Xinyuan-LilyGO/T-Keyboard-S3/examples/Keyboard/Keyboard.ino

#include <Arduino.h>
#include "T-Keyboard_S3_Drive.h"
#include "pin_config.h"
#include "FastLED.h"
#include <USB.h>
#include <USBHIDKeyboard.h>

#define KEY1_SET KEY_LEFT_CTRL
#define KEY2_SET 'c'
#define KEY3_SET 'v'
#define KEY4_SET KEY_BACKSPACE

// #define KEY1_SET 'd'
// #define KEY2_SET 'f'
// #define KEY3_SET 'j'
// #define KEY4_SET 'k'

// How many leds in your strip?
#define NUM_LEDS 4

#define DATA_PIN WS2812B_DATA

// Define the array of leds
CRGB leds[NUM_LEDS];

USBHIDKeyboard Keyboard;

uint8_t KEY1_Lock = 0;
uint8_t KEY1_Press_Delay = 0;
uint8_t KEY2_Lock = 0;
uint8_t KEY2_Press_Delay = 0;
uint8_t KEY3_Lock = 0;
uint8_t KEY3_Press_Delay = 0;
uint8_t KEY4_Lock = 0;
uint8_t KEY4_Press_Delay = 0;

void WS2812B_KEY_Loop(void)
{
    switch (Key1_Flag)
    {
    case 0:
        leds[0] = CRGB::Black;
        FastLED.show();

        Keyboard.release(KEY1_SET);
        KEY1_Press_Delay = 0;
        KEY1_Lock = 0;
        break;
    case 1:
        if (KEY1_Lock == 0)
        {
            leds[0] = CRGB::White;
            FastLED.show();
            Keyboard.press(KEY1_SET);
        }

        if (KEY1_Press_Delay >= 100)
        {
            KEY1_Press_Delay = 100;
            Keyboard.press(KEY1_SET);
        }
        KEY1_Press_Delay++;
        KEY1_Lock = 1;
        break;

    default:
        break;
    }

    switch (Key2_Flag)
    {
    case 0:
        leds[1] = CRGB::Black;
        FastLED.show();

        Keyboard.release(KEY2_SET);
        KEY2_Press_Delay = 0;
        KEY2_Lock = 0;
        break;
    case 1:
        if (KEY2_Lock == 0)
        {
            leds[1] = CRGB::White;
            FastLED.show();
            Keyboard.press(KEY2_SET);
        }

        if (KEY2_Press_Delay >= 100)
        {
            KEY2_Press_Delay = 100;
            Keyboard.press(KEY2_SET);
        }
        KEY2_Press_Delay++;
        KEY2_Lock = 1;
        break;

    default:
        break;
    }

    switch (Key3_Flag)
    {
    case 0:
        leds[2] = CRGB::Black;
        FastLED.show();

        Keyboard.release(KEY3_SET);
        KEY3_Press_Delay = 0;
        KEY3_Lock = 0;
        break;
    case 1:
        if (KEY3_Lock == 0)
        {
            leds[2] = CRGB::White;
            FastLED.show();
            Keyboard.press(KEY3_SET);
        }

        if (KEY3_Press_Delay >= 100)
        {
            KEY3_Press_Delay = 100;
            Keyboard.press(KEY3_SET);
        }
        KEY3_Press_Delay++;
        KEY3_Lock = 1;
        break;

    default:
        break;
    }

    switch (Key4_Flag)
    {
    case 0:
        leds[3] = CRGB::Black;
        FastLED.show();

        Keyboard.release(KEY4_SET);
        KEY4_Press_Delay = 0;
        KEY4_Lock = 0;
        break;
    case 1:
        if (KEY4_Lock == 0)
        {
            leds[3] = CRGB::White;
            FastLED.show();
            Keyboard.press(KEY4_SET);
        }

        if (KEY4_Press_Delay >= 100)
        {
            KEY4_Press_Delay = 100;
            Keyboard.press(KEY4_SET);
        }
        KEY4_Press_Delay++;
        KEY4_Lock = 1;
        break;

    default:
        break;
    }
}

void setup()
{
    T_Keyboard_S3_Key_Initialization();
    FastLED.addLeds<WS2812B, DATA_PIN, GRB>(leds, NUM_LEDS); // GRB ordering is typical
    FastLED.setBrightness(50);

    Keyboard.begin();
    USB.begin();
}

void loop()
{
    WS2812B_KEY_Loop();
}
