Xinyuan-LilyGO/T-Keyboard-S3/examples/GFX_Image/GFX_Image.cpp

/*
 * @Description: None
 * @version: V1.0.0
 * @Author: None
 * @Date: 2023-07-25 13:45:02
 * @LastEditors: LILYGO_L
 * @LastEditTime: 2023-12-19 16:21:23
 * @License: GPL 3.0
 */
#include <Arduino.h>
#include <Arduino_GFX_Library.h>
#include "pin_config.h"
#include "material_24Bit.h"
#include "T-Keyboard_S3_Drive.h"

/* More data bus class: https://github.com/moononournation/Arduino_GFX/wiki/Data-Bus-Class */
Arduino_DataBus *bus = new Arduino_ESP32SPI(
    N085_DC /* DC */, -1 /* CS */, N085_SCLK /* SCK */, N085_MOSI /* MOSI */, -1 /* MISO */); // Software SPI

/* More display class: https://github.com/moononournation/Arduino_GFX/wiki/Display-Class */
Arduino_GFX *gfx = new Arduino_GC9107(
    bus, N085_RST /* RST */, 0 /* rotation */, true /* IPS */,
    128 /* width */, 128 /* height */,
    2 /* col offset 1 */, 1 /* row offset 1 */, 0 /* col_offset2 */, 0 /* row_offset2 */);

void setup(void)
{
    pinMode(N085_BL, OUTPUT);
    ledcAttachPin(N085_BL, 1); // assign TFT_BL pin to channel 1
    ledcSetup(1, 20000, 8);    // 12 kHz PWM, 8-bit resolution
    ledcWrite(1, 255);         // brightness 0 - 255

    N085_Screen_Set(N085_Initialize);

    N085_Screen_Set(N085_Screen_ALL);
    gfx->begin();
    gfx->fillScreen(BLACK);

    N085_Screen_Set(N085_Screen_1);
    gfx->draw24bitRGBBitmap(0, 0, gImage_1, 128, 128); // RGB
    delay(1000);

    N085_Screen_Set(N085_Screen_2);
    gfx->draw24bitRGBBitmap(0, 0, gImage_2, 128, 128); // RGB
    delay(1000);

    N085_Screen_Set(N085_Screen_3);
    gfx->draw24bitRGBBitmap(0, 0, gImage_3, 128, 128); // RGB
    delay(1000);

    N085_Screen_Set(N085_Screen_4);
    gfx->draw24bitRGBBitmap(0, 0, gImage_4, 128, 128); // RGB
    delay(1000);
}

void loop()
{
    for (int i = 255; i > 0; i--)
    {
        ledcWrite(1, i);
        delay(20);
    }
    for (int i = 0; i < 255; i++)
    {
        ledcWrite(1, i);
        delay(20);
    }
}
