Xinyuan-LilyGO/T-Keyboard-S3/examples/Lvgl_UI/google_dinosaur.h

/*
 * @Description: None
 * @version: V1.0.0
 * @Author: LILYGO_L
 * @Date: 2023-11-10 18:21:26
 * @LastEditors: LILYGO_L
 * @LastEditTime: 2023-11-10 18:31:09
 * @License: GPL 3.0
 */
#pragma once

void Google_Dinosaur_Initialization(void);
void Google_Dinosaur_Loop(void);
